flitjes/LedClock/LedClock/ws2812.c

#include <msp430.h>
#include "ws2812.h"

#define OUTPUT_PIN	(0x80)			// Set to whatever UCB0SIMO is on your processor (Px.7 here)

LED leds[NUM_LEDS] = {{0,0,0}};

static uint8_t led_0_offset = 0;

// Initializes everything needed to use this library. This clears the strip.
void initStrip(uint8_t offset){
	/* Disable USCI */
	UCB0CTL1 |= UCSWRST;

	P1SEL |= OUTPUT_PIN;			// configure output pin as SPI output
	P1SEL2 |= OUTPUT_PIN;
	UCB0CTL0 = UCCKPH | UCMSB | UCMST | UCSYNC | UCMODE0; 	// 3-pin, MSB, 8-bit SPI master
	UCB0CTL1 = UCSSEL_2;			// SMCLK source (16 MHz)

	UCB0BR0 = 3;					// 16 MHz / 3 = .1875 us per bit
	UCB0BR1 = 0;
	UCB0CTL1 &= ~UCSWRST;			// Initialize USCI state machine
	led_0_offset = offset;
	clearStrip();					// clear the strip
}

// Sets the color of a certain LED (0 indexed)
void setLEDColor(u_int p, u_char r, u_char g, u_char b){
	if (p >= NUM_LEDS)
		return;
	leds[p].red = r;
	leds[p].green = g;
	leds[p].blue = b;
}

// Send colors to the strip and show them. Disables interrupts while processing.
void showStrip(){
	__bic_SR_register(GIE);       	// disable interrupts
	
	// send RGB color for every LED
	int iled, icolor;
	uint8_t led_count = 0;

	iled= led_0_offset;
	while(led_count < NUM_LEDS){
		u_char rgb[3];

		if(iled >= NUM_LEDS)
			iled = 0;

		rgb[0] = leds[iled].green;
		rgb[1] = leds[iled].red;
		rgb[2] = leds[iled].blue;
		// send green, then red, then blue
		for (icolor = 0; icolor < 3; icolor++){
			u_char mask = 0x80;					// b1000000

			// check each of the 8 bits
			while(mask != 0){
				while (!(IFG2 & UCB0TXIFG));	// wait to transmit

				if (rgb[icolor] & mask){			// most significant bit first
					UCB0TXBUF = HIGH_CODE;		// send 1
				}
				else {
					UCB0TXBUF = LOW_CODE;		// send 0
				}

				mask >>= 1;						// check next bit
			}
		}
		iled++;
		led_count++;
	}
	// send RES code for at least 50 us (800 cycles at 16 MHz)
	_delay_cycles(800);

	__bis_SR_register(GIE);       	// enable interrupts
}

// Clear the color of all LEDs (make them black/off)
void clearStrip(){
	fillStrip(0x00, 0x00, 0x00);	// black
}

// Fill the strip with a solid color. This will update the strip.
void fillStrip(u_char r, u_char g, u_char b){
	int i;
	for (i = 0; i < NUM_LEDS; i++){
		setLEDColor(i, r, g, b);		// set all LEDs to specified color
	}
	showStrip();						// refresh strip
}
