flitjes/LedClock/LedClock/src/grace/Grace_init.c

/*
 *  ======== Grace_init.c ========
 *  DO NOT MODIFY THIS FILE - CHANGES WILL BE OVERWRITTEN
 */

#include <msp430.h>
#include "_Grace.h"

/* verify that the MSP430 headers included support the code that's generated */
#if defined(__TI_COMPILER_VERSION__)
  /* pragma required to suppress TI warning that #warning is unrecognized */
  #pragma diag_suppress 11
#endif
#if __MSP430_HEADER_VERSION__ < 1121
  #if defined(__TI_COMPILER_VERSION__)
    #warn The MSP430 headers included may be incompatible with the generated source files.  If the value of __MSP430_HEADER_VERSION__, declared by msp430.h, is less than 1121, please update your version of the msp430 headers.
  #elif defined(__GNUC__) || defined(__IAR_SYSTEMS_ICC__)
    #warning The MSP430 headers included may be incompatible with the generated source files.  If the value of __MSP430_HEADER_VERSION__, declared by msp430.h, is less than 1121, please update your version of the msp430 headers.
  #else
    /* if we can't just warn, resort to ANSI C's #error */
    #error The MSP430 headers included may be incompatible with the generated source files.  If the value of __MSP430_HEADER_VERSION__, declared by msp430.h, is less than 1121, please update your version of the msp430 headers.
  #endif
#endif
#if defined(__TI_COMPILER_VERSION__)
  /* pragma required to restore TI warnings about unrecognized directives */
  #pragma diag_default 11
#endif

/*
 *  ======== Grace_init =========
 *  Initialize all configured Grace peripherals
 */
void Grace_init(void)
{
    /* Stop watchdog timer from timing out during initial start-up. */
    WDTCTL = WDTPW | WDTHOLD;

    /* initialize Config for the MSP430 GPIO */
    GPIO_graceInit();

    /* initialize Config for the MSP430 2xx family clock systems (BCS) */
    BCSplus_graceInit();

    /* initialize Config for the MSP430 USCI_A0 */
    USCI_A0_graceInit();

    /* initialize Config for the MSP430 USCI_B0 */
    USCI_B0_graceInit();

    /* initialize Config for the MSP430 10-bit Analog to Digital Converter (ADC) */
    ADC10_graceInit();

    /* initialize Interrupt vector support */
    InterruptVectors_graceInit();

    /* initialize Config for the MSP430 System Registers */
    System_graceInit();

    /* initialize Config for the MSP430 A3 Timer0 */
    Timer0_A3_graceInit();

    /* initialize Config for the MSP430 WDT+ */
    WDTplus_graceInit();
}
